mattvenn/fpga-virtual-graf/docs/dell.jpg

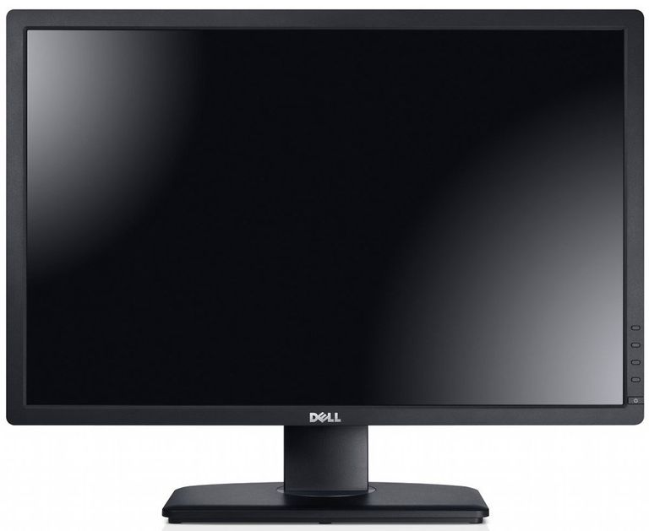
docs/dell.jpg
