mattvenn/fpga-virtual-graf/docs/i2c-read-fail.png

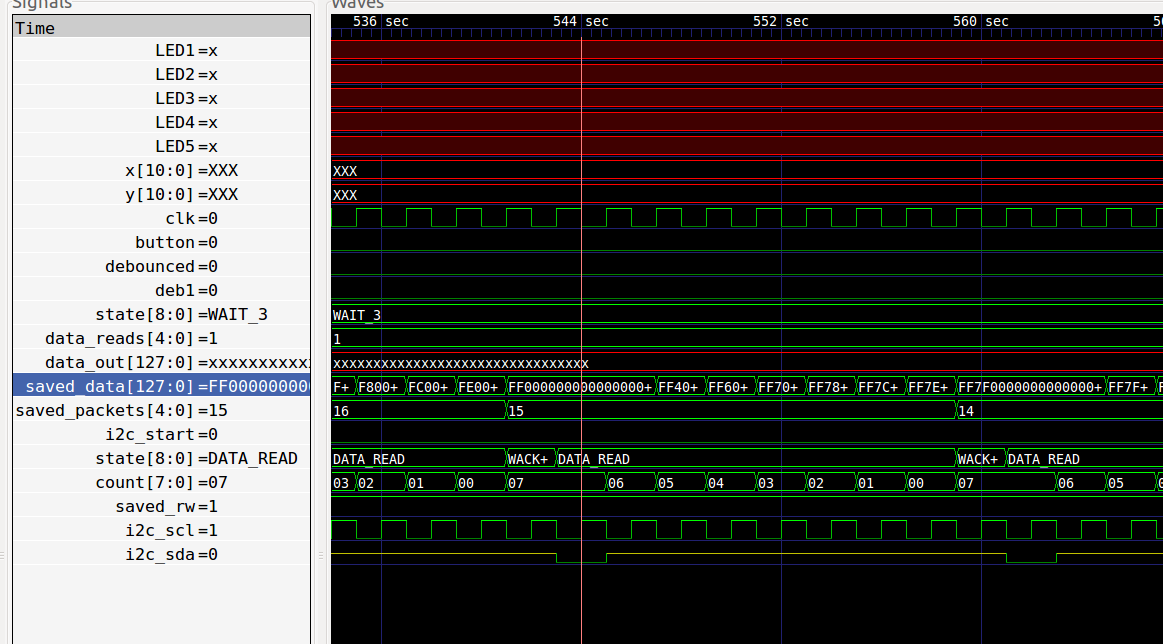
docs/i2c-read-fail.png
