mattvenn/fpga-virtual-graf/docs/sram-trace.png

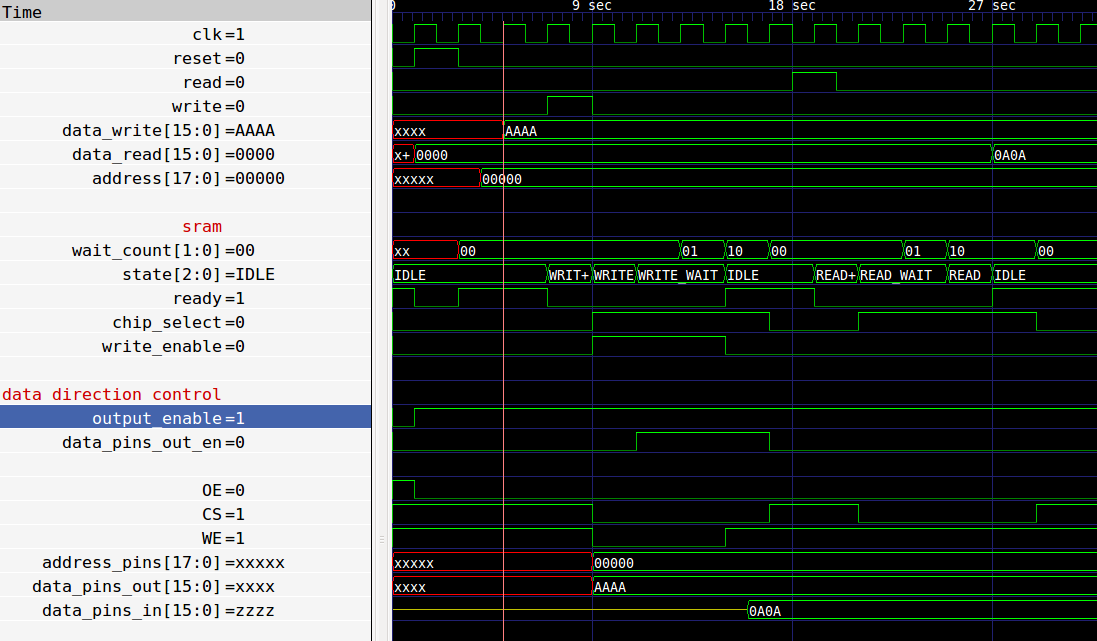
docs/sram-trace.png
