mattvenn/fpga-virtual-graf/src/dvid.v

`default_nettype none
`define enable_output
module dvid (
    input wire clkx5,
    input wire clk,
    input wire hsync,
    input wire vsync,
    input wire blank,
    input wire [2:0] red,
    input wire [2:0] green,
    input wire [2:0] blue,

    output wire [3:0] hdmi_p,
    output wire [3:0] hdmi_n
    );

    wire [1:0] ctls [2:0];
    wire [2:0] colours [2:0];

    reg [9:0] symbols [3:0];
    reg [9:0] high_speed_sr [3:0];
    reg [4:0] high_speed_latch = 5'b00001;
    reg [1:0] output_bits [3:0];

    assign ctls[0] = { vsync, hsync };
    assign colours[0] = red;
    assign colours[1] = green;
    assign colours[2] = blue;

    initial begin
        // clock
        symbols[3] = 10'b0000011111;
    end

    integer i;
	always@(posedge clk) begin
        for(i=0; i<=2; i=i+1) begin
            if(blank == 1'b1) begin
                case(ctls[i])
                    // these are output LSB first so are the reverse as to what is in the spec
                    // hsync and vsync are only sent on blue channel
                    2'b00: symbols[i] <= 10'b1101010100;
                    2'b01: symbols[i] <= 10'b0010101011; // hsync
                    2'b10: symbols[i] <= 10'b0101010100; // vsync
                    default: symbols[i] <= 10'b1010101011;
                endcase
            end else begin
                case(colours[i])
                    3'b000:  symbols[i] <= 10'b0111110000; // 0x10
                    3'b001:  symbols[i] <= 10'b0001001111; // 0x2F
                    3'b010:  symbols[i] <= 10'b0111001100; // 0x54
                    3'b011:  symbols[i] <= 10'b0010001111; // 0x6F
                    3'b100:  symbols[i] <= 10'b0000101111; // 0x8F
                    3'b101:  symbols[i] <= 10'b1000111001; // 0xB4
                    3'b110:  symbols[i] <= 10'b1000011011; // 0xD2
                    default: symbols[i] <= 10'b1011110000; // 0xEF
                endcase
            end
        end
    end

    // from hamster's work, this is missing the output buffer and the 2bit output_bits for each channel
    always@(posedge clkx5) begin
        for(i = 0; i <= 3; i = i + 1) begin
            // 2 bits at a time for DDR
            output_bits[i] <= { high_speed_sr[i][0],high_speed_sr[i][1] }; //, [1:0];
            if(high_speed_latch[0] == 1'b1)
                high_speed_sr[i] <= symbols[i];
            else
                high_speed_sr[i] <= { 2'b00, high_speed_sr[i][9:2] };
        end
        high_speed_latch <= { high_speed_latch[0], high_speed_latch[4:1] };
    end

    // ddr details: http://www.latticesemi.com/view_document?document_id=47960
    `ifdef enable_output
    defparam hdmip0.PIN_TYPE = 6'b010000;
    defparam hdmip0.IO_STANDARD = "SB_LVCMOS" ;
    SB_IO hdmip0 (
    .PACKAGE_PIN(hdmi_p[0]),
    .CLOCK_ENABLE (1'b1  ),
    .OUTPUT_CLK ( clkx5 ),
    .OUTPUT_ENABLE (1'b1 ),
    .D_OUT_0 (output_bits[0][0]), // Non-inverted
    .D_OUT_1 (output_bits[0][1]), // Non-inverted
    );


    // Inverting, N-side of pair
    defparam hdmin0.PIN_TYPE = 6'b010000 ;
    defparam hdmin0.IO_STANDARD = "SB_LVCMOS" ;
    SB_IO hdmin0 (
    .PACKAGE_PIN(hdmi_n[0]),
    .CLOCK_ENABLE ( 1'b1),
    .OUTPUT_CLK (clkx5),
    .OUTPUT_ENABLE (1'b1 ),
    .D_OUT_0 (~output_bits[0][0]), // Inverted
    .D_OUT_1 (~output_bits[0][1]), // Inverted
    );

    // green 
    defparam hdmip1.PIN_TYPE = 6'b010000;
    defparam hdmip1.IO_STANDARD = "SB_LVCMOS" ;
    SB_IO hdmip1 (
    .PACKAGE_PIN(hdmi_p[1]),
    .CLOCK_ENABLE (1'b1  ),
    .OUTPUT_CLK ( clkx5 ),
    .OUTPUT_ENABLE (1'b1 ),
    .D_OUT_0 (output_bits[1][0]), // Non-inverted
    .D_OUT_1 (output_bits[1][1]), // Non-inverted
    );

    // Inverting, N-side of pair
    defparam hdmin1.PIN_TYPE = 6'b010000 ;
    defparam hdmin1.IO_STANDARD = "SB_LVCMOS" ;
    SB_IO hdmin1 (
    .PACKAGE_PIN(hdmi_n[1]),
    .CLOCK_ENABLE ( 1'b1),
    .OUTPUT_CLK (clkx5),
    .OUTPUT_ENABLE (1'b1 ),
    .D_OUT_0 (~output_bits[1][0]), // Inverted
    .D_OUT_1 (~output_bits[1][1]), // Inverted
    );


    // blue 
    defparam hdmip2.PIN_TYPE = 6'b010000;
    defparam hdmip2.IO_STANDARD = "SB_LVCMOS" ;
    SB_IO hdmip2 (
    .PACKAGE_PIN(hdmi_p[2]),
    .CLOCK_ENABLE (1'b1  ),
    .OUTPUT_CLK ( clkx5 ),
    .OUTPUT_ENABLE (1'b1 ),
    .D_OUT_0 (output_bits[2][0]), // Non-inverted
    .D_OUT_1 (output_bits[2][1]), // Non-inverted
    );

    // Inverting, N-side of pair
    defparam hdmin2.PIN_TYPE = 6'b010000 ;
    defparam hdmin2.IO_STANDARD = "SB_LVCMOS" ;
    SB_IO hdmin2 (
    .PACKAGE_PIN(hdmi_n[2]),
    .CLOCK_ENABLE ( 1'b1),
    .OUTPUT_CLK (clkx5),
    .OUTPUT_ENABLE (1'b1 ),
    .D_OUT_0 (~output_bits[2][0]), // Inverted
    .D_OUT_1 (~output_bits[2][1]), // Inverted
    );

    // clock 
    defparam hdmip3.PIN_TYPE = 6'b010000;
    defparam hdmip3.IO_STANDARD = "SB_LVCMOS" ;
    SB_IO hdmip3 (
    .PACKAGE_PIN(hdmi_p[3]),
    .CLOCK_ENABLE (1'b1  ),
    .OUTPUT_CLK ( clkx5 ),
    .OUTPUT_ENABLE (1'b1 ),
    .D_OUT_0 (output_bits[3][0]), // Non-inverted
    .D_OUT_1 (output_bits[3][1]), // Non-inverted
    );

    // Inverting, N-side of pair
    defparam hdmin3.PIN_TYPE = 6'b010000 ;
    defparam hdmin3.IO_STANDARD = "SB_LVCMOS" ;
    SB_IO hdmin3 (
    .PACKAGE_PIN(hdmi_n[3]),
    .CLOCK_ENABLE ( 1'b1),
    .OUTPUT_CLK (clkx5),
    .OUTPUT_ENABLE (1'b1 ),
    .D_OUT_0 (~output_bits[3][0]), // Inverted
    .D_OUT_1 (~output_bits[3][1]), // Inverted
    );

    `endif

endmodule
