mattvenn/fpga-virtual-graf/src/vga.v

/*
generate test pattern at 640 x 480 @ 60Hz

total pixels is 800 x 525 @ 60Hz = 25.2Mhz = 39.6ns

Timings from :

* http://hamsterworks.co.nz/mediawiki/index.php/VGA_timings
* http://web.mit.edu/6.111/www/s2004/NEWKIT/vga.shtml

code adapted from VHDL :

* http://hamsterworks.co.nz/mediawiki/index.php/FPGA_VGA
* http://hamsterworks.co.nz/mediawiki/index.php/Dvid_test#vga.vhd

Horizontal Timing
640     h visible
16      front
96      sync
48      back
800     whole
-       hsync

Vertical Timing

480     v visible
10      front
2       sync
33      back
525     whole
-       vsync

45 blank lines at the bottom, 800 pix wide = 36k clocks for other things

*/
`default_nettype none
module vga (
	input wire clk,
    input wire reset,
    input wire [7:0] pixels,
    output reg [2:0] red,
    output reg [2:0] green,
    output reg [2:0] blue,
    output reg [10:0] hcounter,
    output reg [9:0] vcounter,
    output reg hsync,
    output reg vsync,
    output reg blank,
    output reg lower_blank
    );

    localparam border_w = 10;

	always@(hcounter or vcounter) begin // results in a note about combinatorial logic
        // black everywhere
        red   <= 3'b000;
        green <= 3'b000;
        blue  <= 3'b000;

        // sync
        hsync <= 1'b1;
        vsync <= 1'b1;
        blank <= 1'b0;
        lower_blank <= 1'b0;

        // sync pulses
        if(hcounter > 655 && hcounter < 751)
           hsync <= 1'b0;
        if(vcounter > 489 && vcounter < 491)
           vsync <= 1'b0;
        // blank is whenever outside of viewable area
        if(hcounter > 639 || vcounter > 479)
           blank <= 1'b1;
        if(vcounter > 479 )
           lower_blank <= 1'b1;

        // top and bottom border
        if(vcounter < border_w || ( vcounter > 480 - border_w && vcounter < 480)) begin
                red <= 3'b111;
                green <= 3'b000;
                blue <= 3'b111;
        end else // left and right border
        if(hcounter < border_w || ( hcounter > 640 - border_w && hcounter < 640)) begin
            red <= 3'b111;
            green <= 3'b000;
            blue <= 3'b111;
        end else // data from pixel register
        if(pixels[hcounter])  begin
            red <= 3'b000;
            green <= 3'b111;
            blue <= 3'b111;
        end 

    end

    // increment counters and wrap them
    always@(posedge clk) begin
        if(reset == 1) begin
            hcounter <= 0;
            vcounter <= 0;
        end else if(hcounter == 799) begin
            hcounter <= 0;
            if(vcounter == 524) begin
                vcounter <= 0;
            end else
                vcounter <= vcounter + 1;
            end
        else
            hcounter <= hcounter + 1;
    end
endmodule
