mattvenn/fpga-virtual-graf/tests/camera_tb.v

`default_nettype none
module test;

  reg reset = 0;
  wire i2c_sda;
  wire i2c_scl;

  initial begin
     $dumpfile("test.vcd");
     $dumpvars(0,test);
     # 2 reset = 0;
     # 4000;
     $finish;
  end

  // clock
  reg clk = 0;
  always #1 clk = !clk;

  camera cam(.clk_en(1), .clk (clk), .reset (reset), .i2c_scl(i2c_scl), .i2c_sda(i2c_sda) ); 

endmodule // test
